antennaforge/10m-3el-phased-array-yagi/images/elements/element-clamp.jpeg

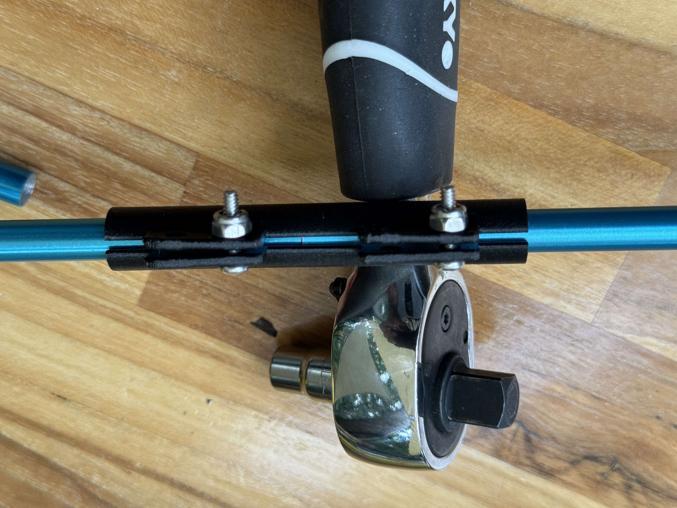
images/elements/element-clamp.jpeg
