antennaforge/10m-3el-phased-array-yagi/images/stl/10m-yagi-boom-mast-clamp.png

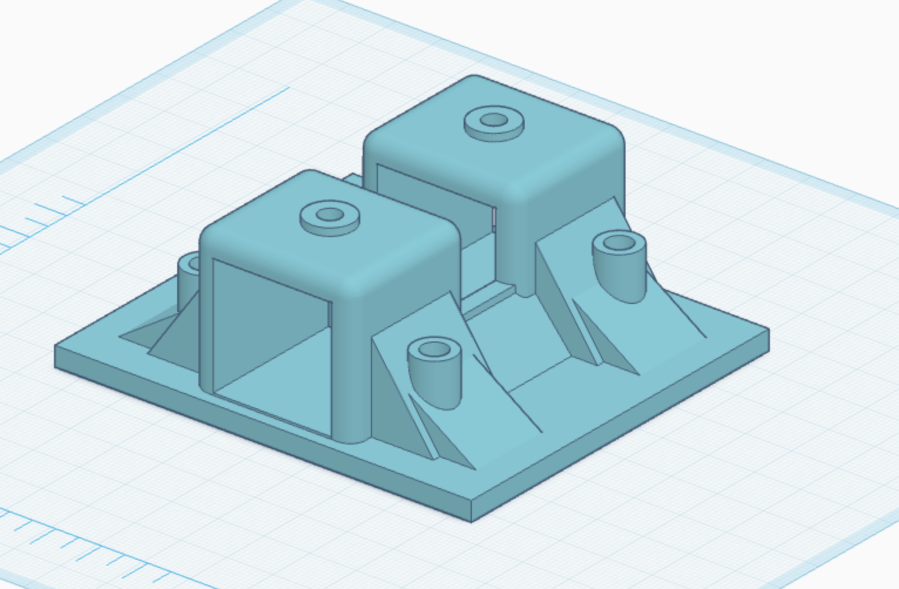
images/stl/10m-yagi-boom-mast-clamp.png
