antennaforge/10m-3el-phased-array-yagi/images/truss/tensioner-clip.jpeg

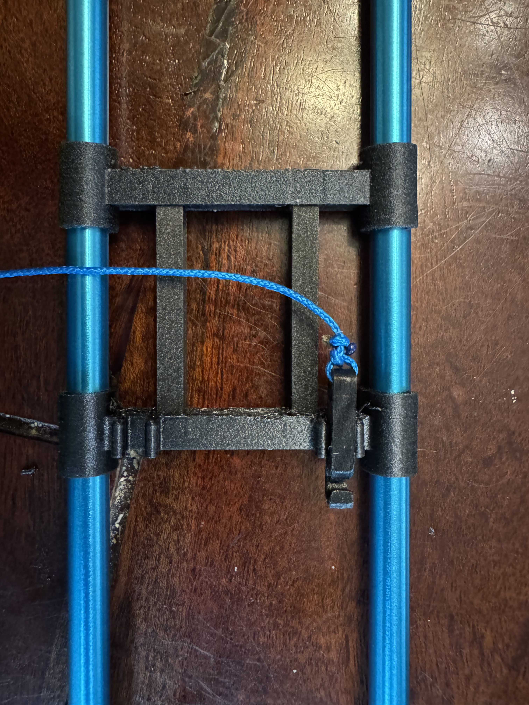
images/truss/tensioner-clip.jpeg
