antennaforge/10m-3el-phased-array-yagi/images/testing/argentina-signal.png

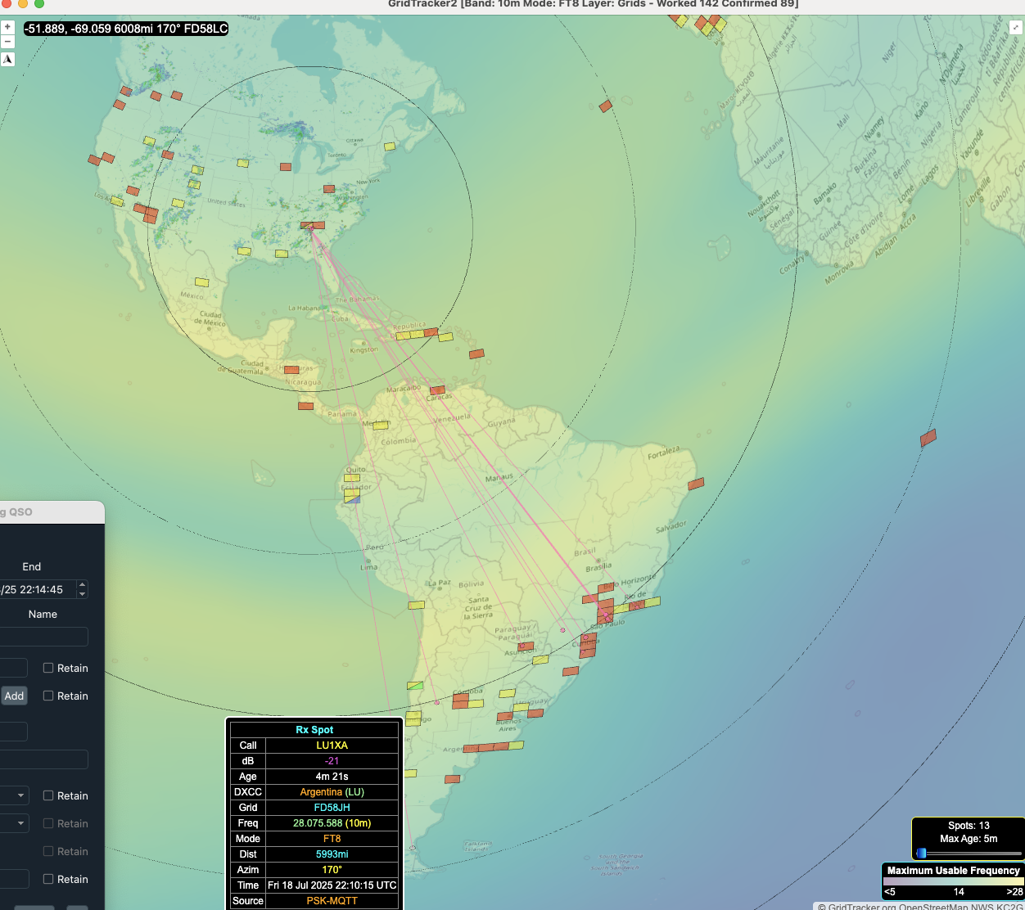
images/testing/argentina-signal.png
