antennaforge/10m-3el-phased-array-yagi/images/testing/argentina.png

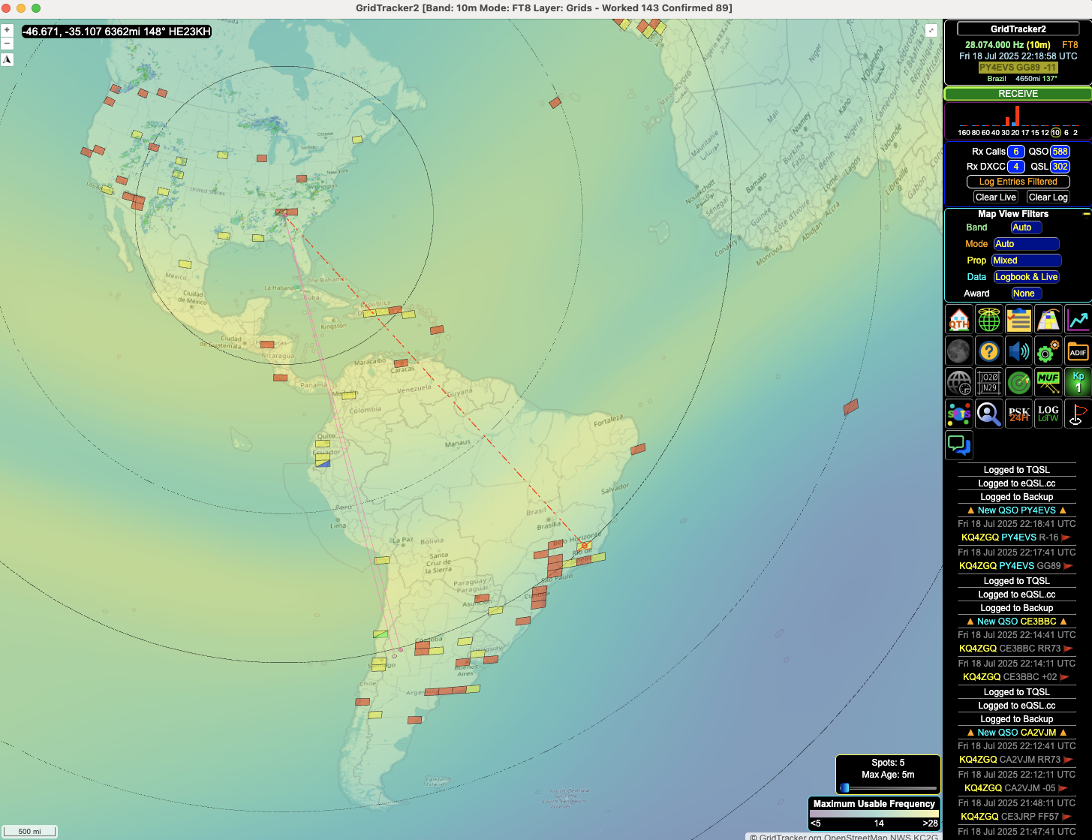
images/testing/argentina.png
