antennaforge/10m-3el-phased-array-yagi/images/testing/chile2.png

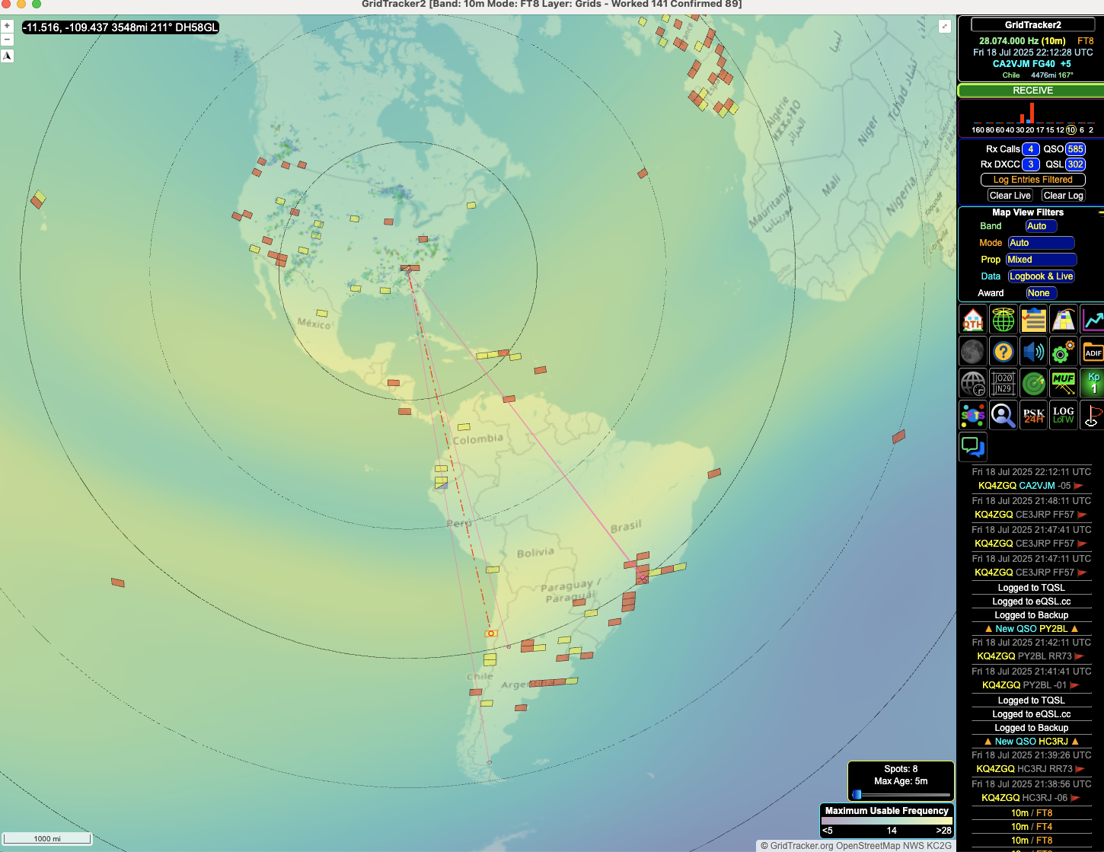
images/testing/chile2.png
