antennaforge/10m-3el-phased-array-yagi/images/testing/new-caledonia.png

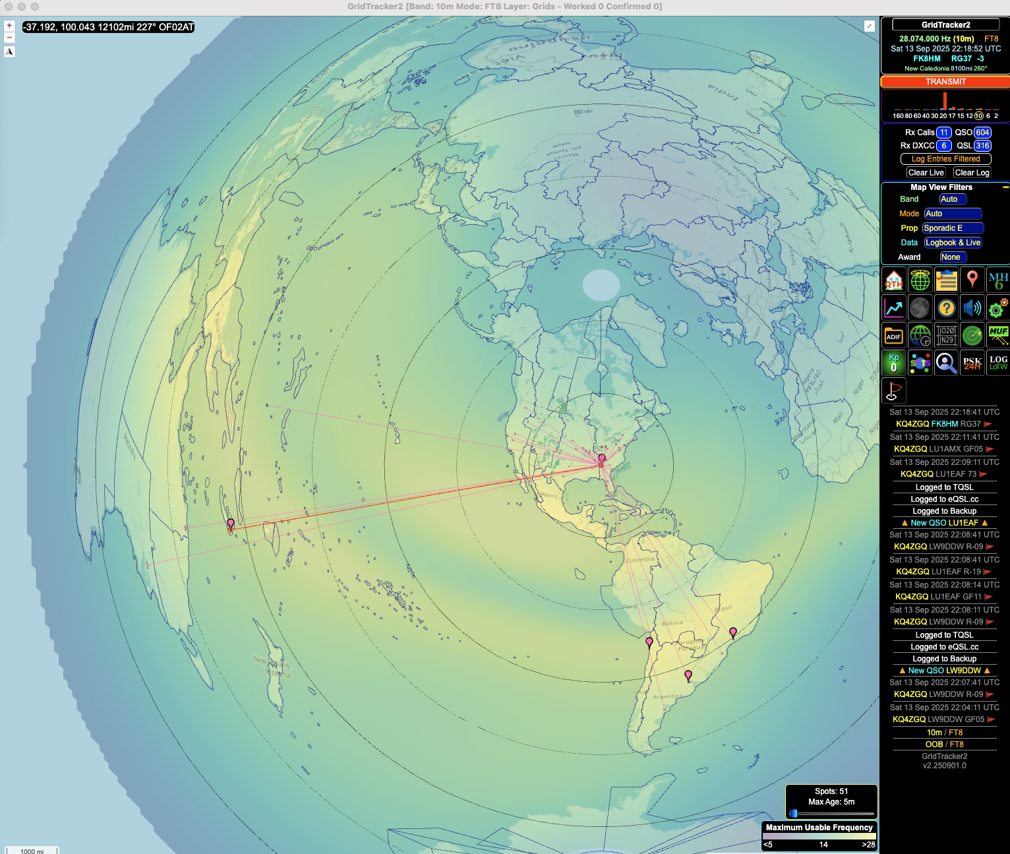
images/testing/new-caledonia.png
