antennaforge/10m-3el-phased-array-yagi/images/testing/uruguay-signal.png

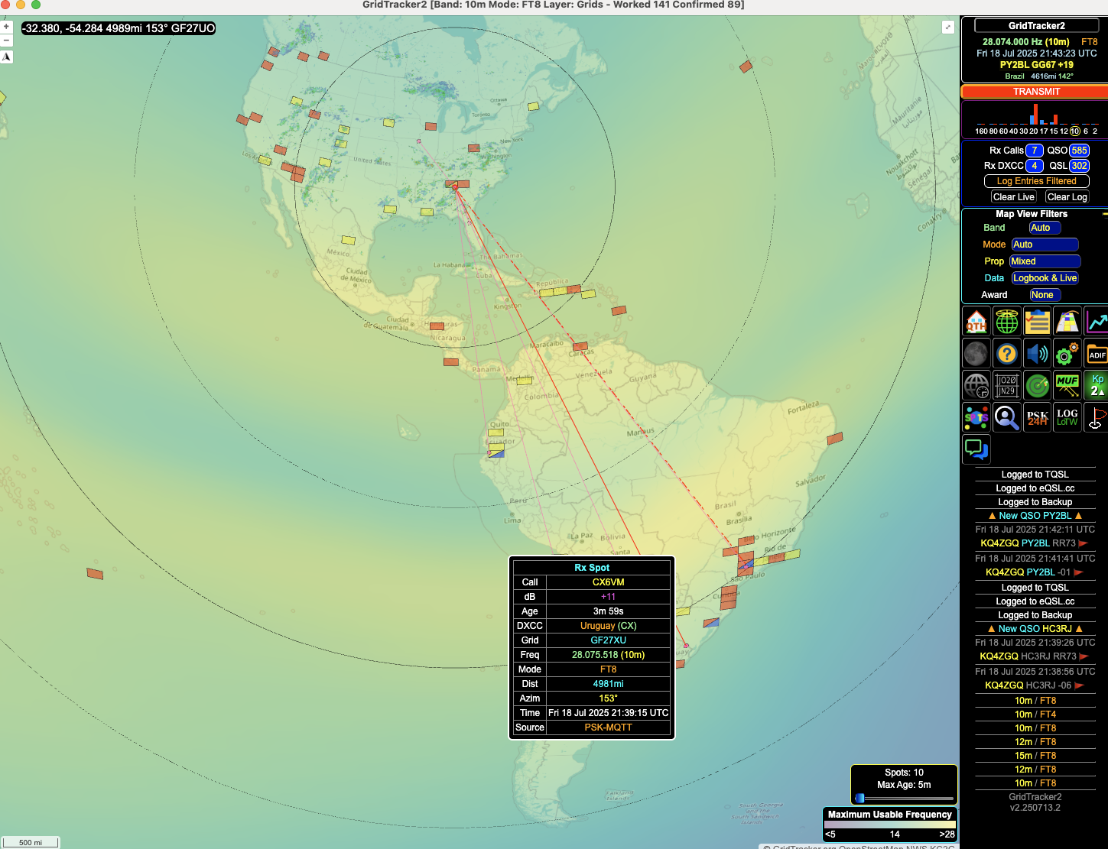
images/testing/uruguay-signal.png
