antennaforge/10m-3el-phased-array-yagi/images/elements/element-arrow-connector1.jpeg

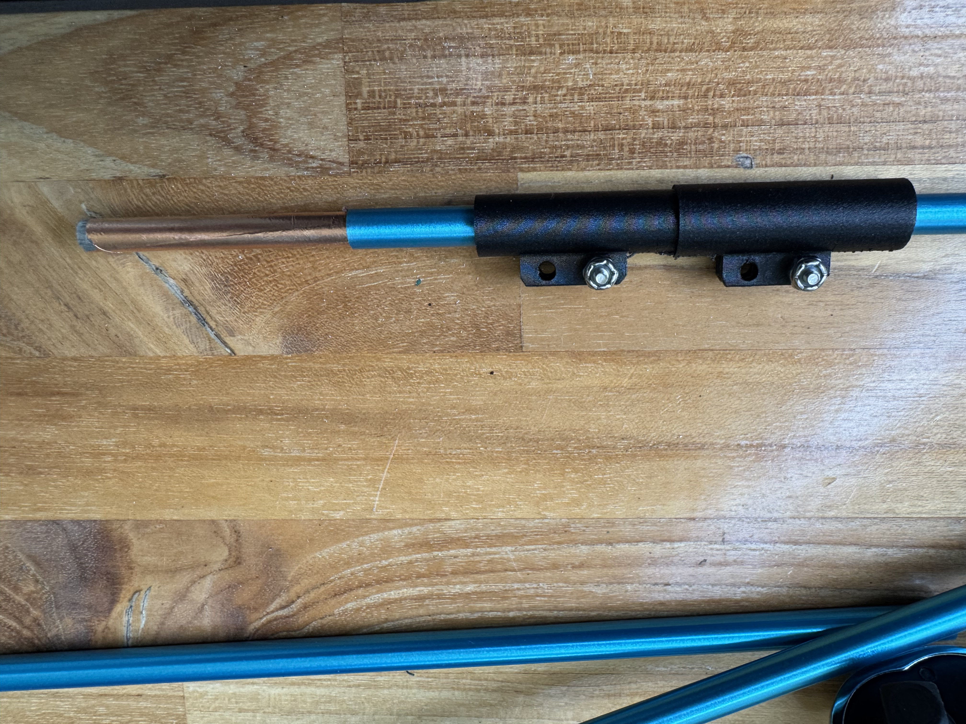
images/elements/element-arrow-connector1.jpeg
