antennaforge/10m-3el-phased-array-yagi/images/mast/boom-mast-section.jpeg

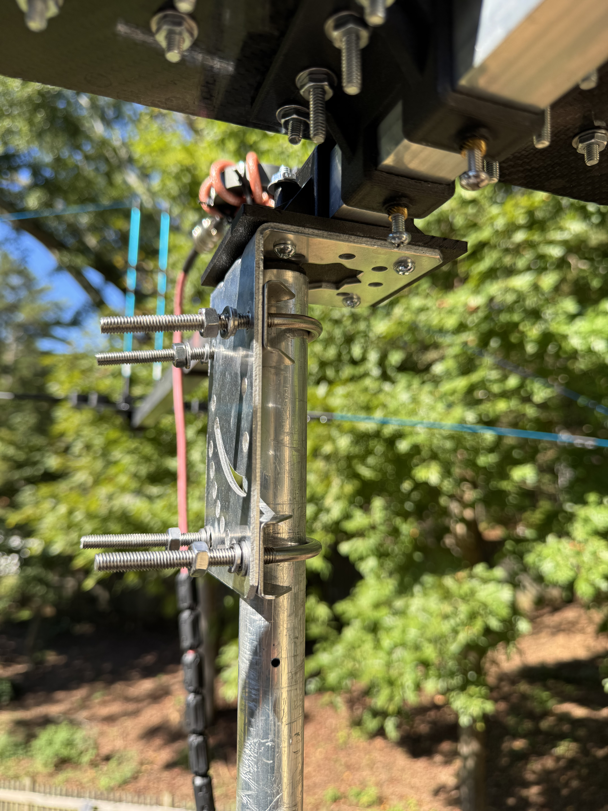
images/mast/boom-mast-section.jpeg
